UCSD-Optics-Maze-Educational-Games/CosmicWhisper/images/substances_chart.png

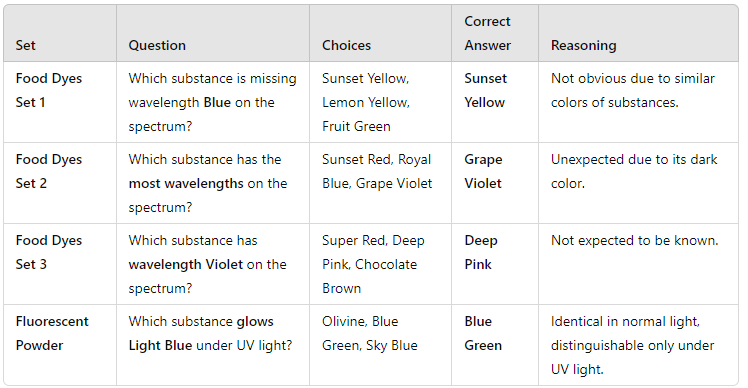
images/substances_chart.png
