UCSD-Optics-Maze-Educational-Games/CosmicWhisper/CAD Files/.step Files/board leg.step

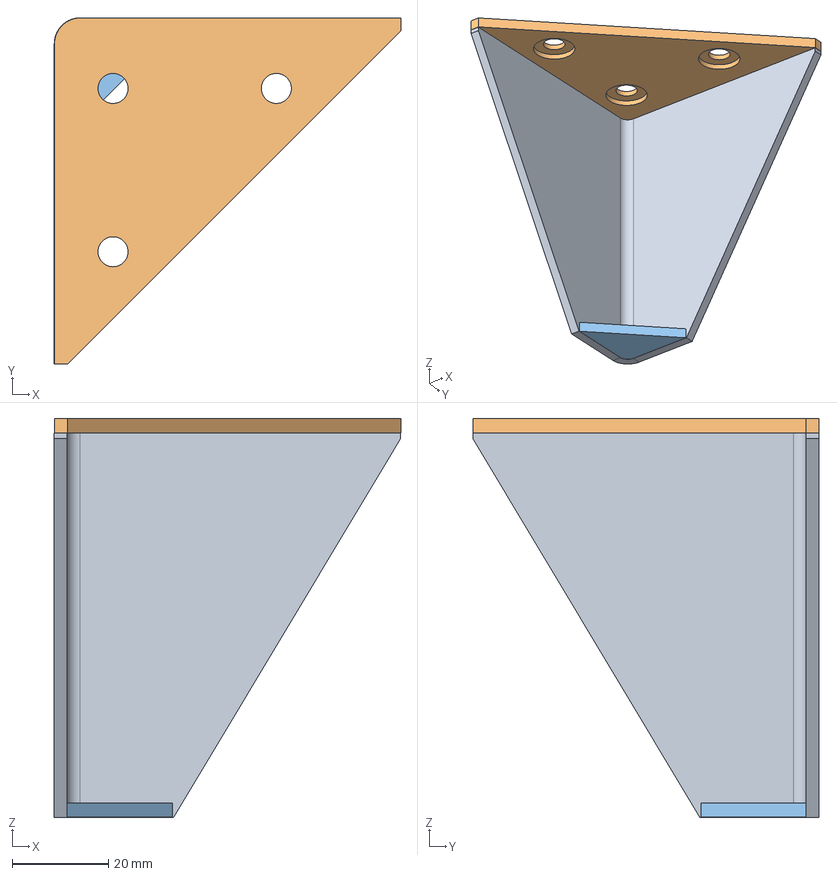
[picture p32: CAD file, 2025-08-17]
CAD Files/.step Files/board leg.step
72.1 x 72.1 x 83.1 mm
