UCSD-Optics-Maze-Educational-Games/CosmicWhisper/CAD Files/CosmicWhisper.kicad_sch

## KiCad design CAD Files/CosmicWhisper.kicad_sch (2025-08-21)

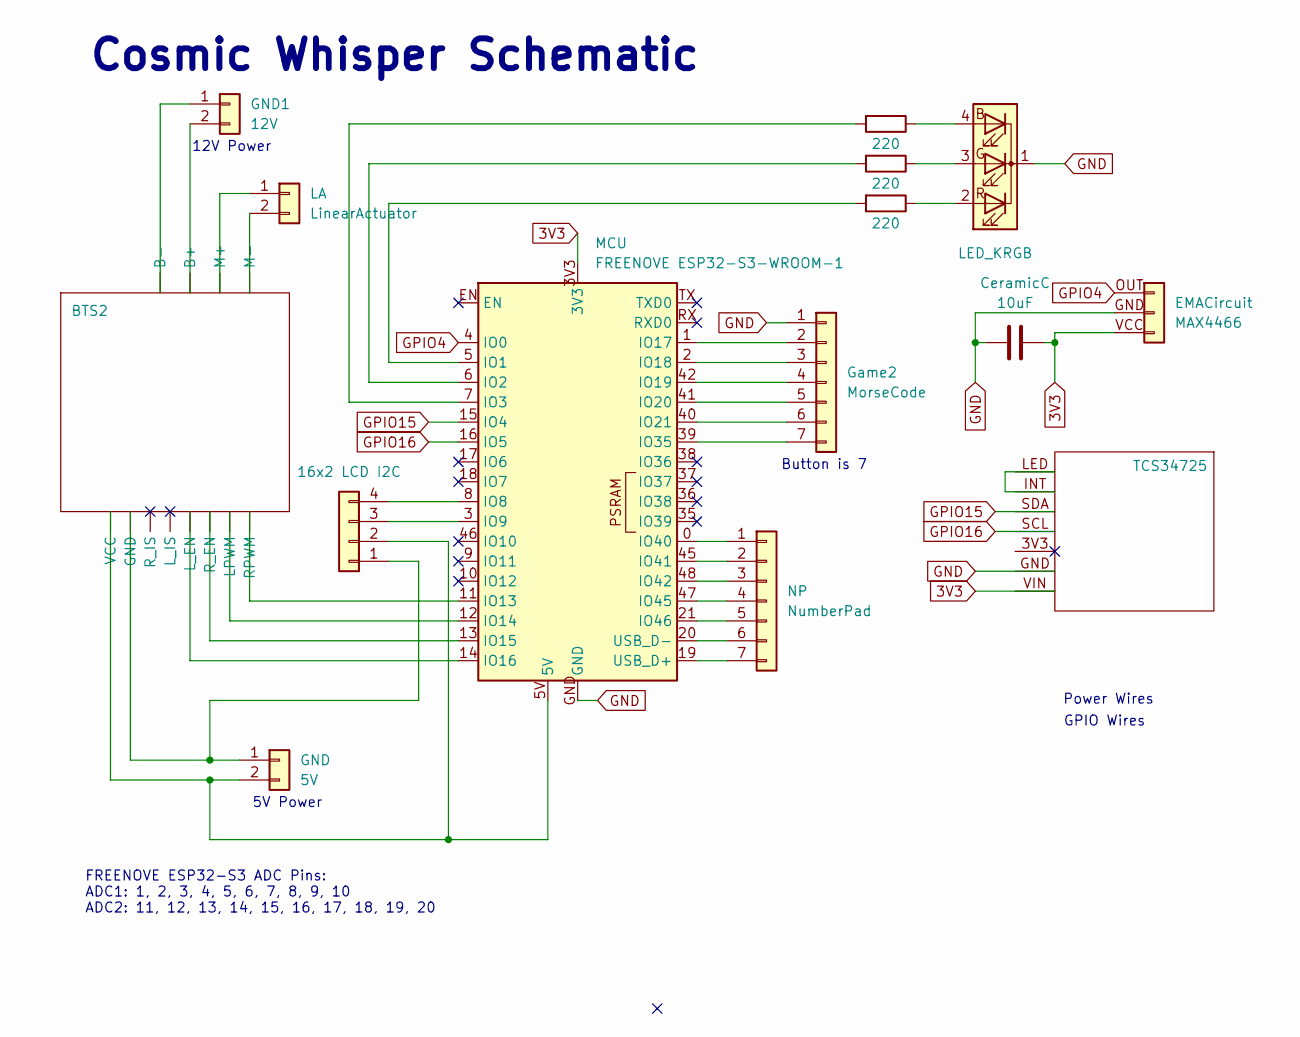
[picture p33: schematic CosmicWhisper.kicad_sch]

Parts:
BTS2: (no value)
CeramicC: 10uF
D2: LED_KRGB
EMACircuit: MAX4466
GND: 5V
GND1: 12V
Game2: MorseCode
J1: 16x2 LCD I2C
LA: LinearActuator
MCU: FREENOVE ESP32-S3-WROOM-1; ESP32-S3-WROOM-1
NP: NumberPad
R1, R2, R3: 220
TCS34725: (no value)

Connections:
3V3: CeramicC.2, EMACircuit.VCC (Pin_3), MCU.3V3, TCS34725.VIN
GND: CeramicC.1, D2.1 (K), EMACircuit.GND (Pin_2), Game2.1, MCU.40 (GND), MCU.41 (GND), MCU.GND, TCS34725.GND
GPIO4: EMACircuit.OUT (Pin_1), MCU.4 (IO0)
GPIO15: MCU.15 (IO4), TCS34725.SDA
GPIO16: MCU.16 (IO5), TCS34725.SCL
unnamed: BTS2., GND.1, GND.2, GND1.1, GND1.2, J1.1, J1.2, LA.1, LA.2, MCU.5V, MCU.11 (IO13), MCU.12 (IO14), MCU.13 (IO15), MCU.14 (IO16)
unnamed: D2.2 (RA), R1.1
unnamed: D2.3 (GA), R2.1
unnamed: D2.4 (BA), R3.1
unnamed: Game2.2, MCU.1 (IO17)
unnamed: Game2.3, MCU.2 (IO18)
unnamed: Game2.4, MCU.42 (IO19)
unnamed: Game2.5, MCU.41 (GND)
unnamed: Game2.6, MCU.40 (GND)
unnamed: Game2.7, MCU.39 (IO35)
unnamed: J1.3, MCU.3 (IO9)
unnamed: J1.4, MCU.8 (IO8)
unnamed: MCU.0 (IO40), NP.1
unnamed: MCU.5 (IO1), R1.2
unnamed: MCU.6 (IO2), R2.2
unnamed: MCU.7 (IO3), R3.2
unnamed: MCU.19 (USB_D+), NP.7
unnamed: MCU.20 (USB_D-), NP.6
unnamed: MCU.21 (IO46), NP.5
unnamed: MCU.45 (IO41), NP.2
unnamed: MCU.47 (IO45), NP.4
unnamed: MCU.48 (IO42), NP.3
unnamed: TCS34725.INT, TCS34725.LED

Notes on the sheet:
GPIO Wires
5V Power
FREENOVE ESP32-S3 ADC Pins: ADC1: 1, 2, 3, 4, 5, 6, 7, 8, 9, 10 ADC2: 11, 12, 13, 14, 15, 16, 17, 18, 19, 20
Button is 7
Power Wires
Cosmic Whisper Schematic
12V Power
